jamesbowman/spidriver/images/DSC_1315a.JPG

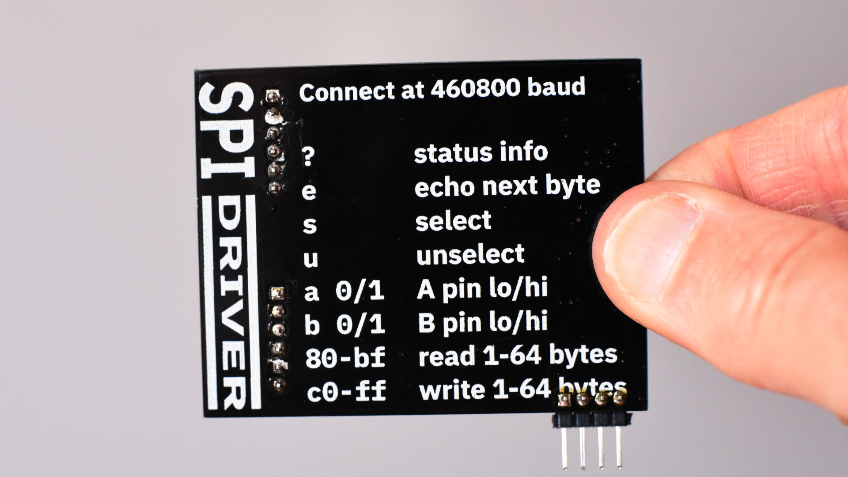
images/DSC_1315a.JPG
