jamesbowman/spidriver/python/samples/crowdsupply.png

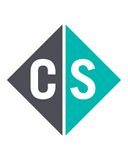
python/samples/crowdsupply.png
