jamesbowman/spidriver/python/samples/grace-hopper.jpg

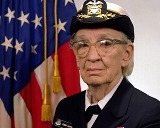
python/samples/grace-hopper.jpg
