jamesbowman/spidriver/python/samples/grace.png

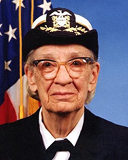
python/samples/grace.png
