jamesbowman/spidriver/python/samples/mandrill.jpg

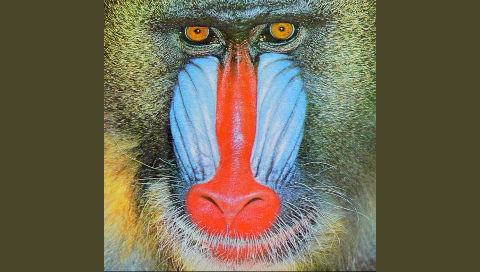
python/samples/mandrill.jpg
