jamesbowman/spidriver/c/win32gui/include/Resource.h

#pragma once

#define FONT_LARGE                      50

#define IDI_APPICON                     101
#define IDR_MAINMENU                    102
#define IDR_ACCELERATOR                 103
#define IDD_ABOUTDIALOG                 104
#define IDD_DIALOG1                     105
#define BTN_A                           106
#define BTN_B                           107
#define BTN_CS                          108
#define EDIT_TX                         109
#define BTN_TX                          110
#define MISO_LOG                        111
#define MOSI_LOG                        112

#define INF_V                           200
#define INF_C                           201
#define INF_T                           202
#define INF_U                           203
#define INF_S                           204

#define EVT_T                           300

#define COMBO_DEV                        400

#define ID_FILE_EXIT                    40001
#define ID_HELP_ABOUT                   40002

#ifndef IDC_STATIC
  #define IDC_STATIC                    -1
#endif
