jamesbowman/spidriver/c/win32gui/src/example.c

#include <stdio.h>
#include "serialport.h"
int main(void)
{
    HANDLE h = openSerialPort("COM3",B460800,one,off);
    char sendbuffer[] = "test";
    char readbuffer[100];
    //write test
    int bytesWritten = writeToSerialPort(h,sendbuffer,strlen(sendbuffer));
    printf("%d Bytes were written\n",bytesWritten);
    //read something
    int bytesRead = readFromSerialPort(h,readbuffer,99);
    readbuffer[bytesRead]=0;
    printf("%d Bytes were read:%s\n",bytesRead,readbuffer);
    closeSerialPort(h);
    return 0;
}
